esar/hdmilight-v2/firmware/cmd_i2c.c

/*

   Copyright (C) 2013 Stephen Robinson
  
   This file is part of HDMI-Light
  
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
*/

#include <inttypes.h>
#include <avr/io.h>
#include <avr/pgmspace.h>
#include <string.h>
#include <stdio.h>
#include "ambilight.h"
#include "i2c.h"

#include "config_hdmi.h"
#include "config_edid.h"


uint8_t i2cRead(uint8_t addr, uint8_t subaddr)
{
	int val;
	i2c_start();
	i2c_write(addr);
	i2c_write(subaddr);
	i2c_start();
	i2c_write(addr + 1);
	val = i2c_read();
	i2c_stop();

	return val;
}

void i2cWrite(uint8_t addr, uint8_t subaddr, uint8_t value)
{
	i2c_start();
	i2c_write(addr);
	i2c_write(subaddr);
	i2c_write(value);
	i2c_stop();
}

void cmdSetI2C(uint8_t argc, char** argv)
{
	if(argc == 4)
	{
		i2cWrite(getint(&argv[1]), getint(&argv[2]), getint(&argv[3]));
		printf_P(PSTR("OK\n"));
	}
}

void cmdGetI2C(uint8_t argc, char** argv)
{
	if(argc == 3)
	{
		int val = i2cRead(getint(&argv[1]), getint(&argv[2]));
		printf_P(PSTR("Read: %d (0x%02x)\n"), val, val);
	}
	else if(argc == 4)
	{
		uint8_t minBit, maxBit;
		int val = i2cRead(getint(&argv[1]), getint(&argv[2]));
		
		getrange(argv[3], &minBit, &maxBit);
		if(maxBit < minBit)
		{
			uint8_t tmp = maxBit;
			maxBit = minBit;
			minBit = tmp;
		}

		val >>= minBit;
		val &= (1 << (maxBit - minBit + 1)) - 1;
		
		printf_P(PSTR("Read: %d (0x%02x)\n"), val, val);
	}
}

void writeEdid(const char* edid, int length)
{
	int i;

	for(i = 0; i < length; ++i)
		i2cWrite(0x6c, i, pgm_read_byte(&edid[i]));
}

void writeConfig(const struct ConfigTable* table)
{
	const struct ConfigTable* p;

	for(p = table; pgm_read_byte(&p->address) != 0; ++p)
	{
		unsigned char address = pgm_read_byte(&p->address);
		unsigned char subaddress = pgm_read_byte(&p->subaddress);
		unsigned char data = pgm_read_byte(&p->data);

		if(!silent)
		{
			printf_P(PSTR("%d %d %d : "), address, subaddress, data);
			i2c_start();
			printf_P(PSTR("%s "), i2c_write(address)    ? "ACK" : "NACK");
			printf_P(PSTR("%s "), i2c_write(subaddress) ? "ACK" : "NACK");
			printf_P(PSTR("%s\n"), i2c_write(data)      ? "ACK" : "NACK");
			i2c_stop();
		}
		else
			i2cWrite(address, subaddress, data);
	}
}

void cmdRstI2C(uint8_t argc, char** argv)
{
	writeConfig(g_configTablePreEdid);
	writeEdid(g_edid, sizeof(g_edid));
	writeConfig(g_configTablePostEdid);
}
